simonyiszk/ZetaSDR/zetasdr-fw-stm32/Core/Inc/tusb_config.h

/*
 * The MIT License (MIT)
 *
 * Copyright (c) 2019 Ha Thach (tinyusb.org)
 *
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
 */

#ifndef _TUSB_CONFIG_H_
#define _TUSB_CONFIG_H_

#include "zetasdr_descriptor.h"

#ifdef __cplusplus
extern "C" {
#endif

//--------------------------------------------------------------------+
// Board Specific Configuration
//--------------------------------------------------------------------+

// RHPort number used for device can be defined by board.mk, default to port 0
#ifndef BOARD_TUD_RHPORT
#define BOARD_TUD_RHPORT      0
#endif

// RHPort max operational speed can defined by board.mk
#ifndef BOARD_TUD_MAX_SPEED
#define BOARD_TUD_MAX_SPEED   OPT_MODE_DEFAULT_SPEED
#endif

//--------------------------------------------------------------------
// COMMON CONFIGURATION
//--------------------------------------------------------------------

// defined by compiler flags for flexibility
#ifndef CFG_TUSB_MCU
#error CFG_TUSB_MCU must be defined
#endif

#ifndef CFG_TUSB_OS
#define CFG_TUSB_OS               OPT_OS_NONE
#endif

#ifndef CFG_TUSB_DEBUG
#define CFG_TUSB_DEBUG            0
#endif

// Enable Device stack
#define CFG_TUD_ENABLED           1

// Default is max speed that hardware controller could support with on-chip PHY
#define CFG_TUD_MAX_SPEED         BOARD_TUD_MAX_SPEED

/* USB DMA on some MCUs can only access a specific SRAM region with restriction on alignment.
 * Tinyusb use follows macros to declare transferring memory so that they can be put
 * into those specific section.
 * e.g
 * - CFG_TUSB_MEM SECTION : __attribute__ (( section(".usb_ram") ))
 * - CFG_TUSB_MEM_ALIGN   : __attribute__ ((aligned(4)))
 */
#ifndef CFG_TUSB_MEM_SECTION
#define CFG_TUSB_MEM_SECTION
#endif

#ifndef CFG_TUSB_MEM_ALIGN
#define CFG_TUSB_MEM_ALIGN        __attribute__ ((aligned(4)))
#endif

//--------------------------------------------------------------------
// DEVICE CONFIGURATION
//--------------------------------------------------------------------

#ifndef CFG_TUD_ENDPOINT0_SIZE
#define CFG_TUD_ENDPOINT0_SIZE    64
#endif

//------------- CLASS -------------//
#define CFG_TUD_AUDIO             1
#define CFG_TUD_CDC               1
#define CFG_TUD_MSC               0
#define CFG_TUD_HID               0
#define CFG_TUD_MIDI              0
#define CFG_TUD_VENDOR            0

//--------------------------------------------------------------------
// AUDIO CLASS DRIVER CONFIGURATION
//--------------------------------------------------------------------

// Have a look into audio_device.h for all configurations
#define CFG_TUD_AUDIO_FUNC_1_SAMPLE_RATE              192000

#define CFG_TUD_AUDIO_FUNC_1_DESC_LEN                 TUD_SDR_IQ_DESC_LEN //TUD_AUDIO_MIC_FOUR_CH_DESC_LEN // IQ_descriptor hossza

#define CFG_TUD_AUDIO_FUNC_1_N_AS_INT                 1
#define CFG_TUD_AUDIO_FUNC_1_CTRL_BUF_SZ              64

#define CFG_TUD_AUDIO_ENABLE_EP_IN                    1
#define CFG_TUD_AUDIO_FUNC_1_N_BYTES_PER_SAMPLE_TX    2         // This value is not required by the driver, it parses this information from the descriptor once the alternate interface is set by the host - we use it for the setup
#define CFG_TUD_AUDIO_FUNC_1_N_CHANNELS_TX            2         // This value is not required by the driver, it parses this information from the descriptor once the alternate interface is set by the host - we use it for the setup
#define CFG_TUD_AUDIO_EP_SZ_IN                        TUD_AUDIO_EP_SIZE(CFG_TUD_AUDIO_FUNC_1_SAMPLE_RATE, CFG_TUD_AUDIO_FUNC_1_N_BYTES_PER_SAMPLE_TX, CFG_TUD_AUDIO_FUNC_1_N_CHANNELS_TX)

#define CFG_TUD_AUDIO_ENABLE_ENCODING                 0
#define CFG_TUD_AUDIO_EP_IN_FLOW_CONTROL              1

#if CFG_TUD_AUDIO_ENABLE_ENCODING

#define CFG_TUD_AUDIO_FUNC_1_EP_IN_SZ_MAX             CFG_TUD_AUDIO_EP_SZ_IN
#define CFG_TUD_AUDIO_FUNC_1_EP_IN_SW_BUF_SZ          CFG_TUD_AUDIO_EP_SZ_IN

#define CFG_TUD_AUDIO_ENABLE_TYPE_I_ENCODING          1
#define CFG_TUD_AUDIO_FUNC_1_CHANNEL_PER_FIFO_TX      2         // One I2S stream contains two channels, each stream is saved within one support FIFO - this value is currently fixed, the driver does not support a changing value
#define CFG_TUD_AUDIO_FUNC_1_N_TX_SUPP_SW_FIFO        (CFG_TUD_AUDIO_FUNC_1_N_CHANNELS_TX / CFG_TUD_AUDIO_FUNC_1_CHANNEL_PER_FIFO_TX)
#define CFG_TUD_AUDIO_FUNC_1_TX_SUPP_SW_FIFO_SZ       (TUD_OPT_HIGH_SPEED ? 32 : 4) * (CFG_TUD_AUDIO_EP_SZ_IN / CFG_TUD_AUDIO_FUNC_1_N_TX_SUPP_SW_FIFO) // Example write FIFO every 1ms, so it should be 8 times larger for HS device

#else

#define CFG_TUD_AUDIO_FUNC_1_EP_IN_SZ_MAX             CFG_TUD_AUDIO_EP_SZ_IN
#define CFG_TUD_AUDIO_FUNC_1_EP_IN_SW_BUF_SZ          (TUD_OPT_HIGH_SPEED ? 32 : 4) * CFG_TUD_AUDIO_EP_SZ_IN // Example write FIFO every 1ms, so it should be 8 times larger for HS device

#endif

// CDC FIFO size of TX and RX
#define CFG_TUD_CDC_RX_BUFSIZE                    64
#define CFG_TUD_CDC_TX_BUFSIZE                    64

#ifdef __cplusplus
}
#endif

#endif /* _TUSB_CONFIG_H_ */
