simonyiszk/ZetaSDR/zetasdr-fw-stm32/Core/Src/audio.c

#include "tusb.h"
#include "audio.h"
#include "adc.h"
#include "tim.h"

//--------------------------------------------------------------------+
// AUDIO Task
//--------------------------------------------------------------------+

// Audio controls
// Current states
bool mute[CFG_TUD_AUDIO_FUNC_1_N_CHANNELS_TX + 1]; 				        // +1 for master channel 0
uint16_t volume[CFG_TUD_AUDIO_FUNC_1_N_CHANNELS_TX + 1]; 					// +1 for master channel 0
uint32_t sampFreq;
uint8_t clkValid;

// Range states
audio_control_range_2_n_t(1) volumeRng[CFG_TUD_AUDIO_FUNC_1_N_CHANNELS_TX+1]; 			// Volume range state
audio_control_range_4_n_t(1) sampleFreqRng; 						// Sample frequency range state

#if CFG_TUD_AUDIO_ENABLE_ENCODING
// Audio test data, each buffer contains 2 channels, buffer[0] for CH0-1, buffer[1] for CH1-2
uint16_t i2s_dummy_buffer[CFG_TUD_AUDIO_FUNC_1_N_TX_SUPP_SW_FIFO][CFG_TUD_AUDIO_FUNC_1_N_CHANNELS_TX*CFG_TUD_AUDIO_FUNC_1_SAMPLE_RATE/1000/CFG_TUD_AUDIO_FUNC_1_N_TX_SUPP_SW_FIFO];
#else
// Audio data, double buffering to reduce glitches
volatile uint16_t buffer_a[CFG_TUD_AUDIO_FUNC_1_N_CHANNELS_TX*CFG_TUD_AUDIO_FUNC_1_SAMPLE_RATE/1000];
volatile uint16_t buffer_b[CFG_TUD_AUDIO_FUNC_1_N_CHANNELS_TX*CFG_TUD_AUDIO_FUNC_1_SAMPLE_RATE/1000];
volatile uint16_t *buf_record, *buf_stream;
#endif

void audio_init(void){
  
  sampFreq = AUDIO_SAMPLE_RATE;
  clkValid = 1;

  sampleFreqRng.wNumSubRanges = 1;
  sampleFreqRng.subrange[0].bMin = AUDIO_SAMPLE_RATE;
  sampleFreqRng.subrange[0].bMax = AUDIO_SAMPLE_RATE;
  sampleFreqRng.subrange[0].bRes = 0;

  // Generate dummy data
#if CFG_TUD_AUDIO_ENABLE_ENCODING
  uint16_t * p_buff = i2s_dummy_buffer[0];
  uint16_t dataVal = 0;
  for (uint16_t cnt = 0; cnt < AUDIO_SAMPLE_RATE/1000; cnt++)
  {
    // CH0 saw wave
    *p_buff++ = dataVal;
    // CH1 inverted saw wave
    *p_buff++ = 3200 + AUDIO_SAMPLE_RATE/1000 - dataVal;
    dataVal+= 32;
  }
  p_buff = i2s_dummy_buffer[1];
  for (uint16_t cnt = 0; cnt < AUDIO_SAMPLE_RATE/1000; cnt++)
  {
    // CH3 square wave
    *p_buff++ = cnt < (AUDIO_SAMPLE_RATE/1000/2) ? 3400:5000;
    // CH4 sinus wave
    float t = 2*3.1415f * cnt / (AUDIO_SAMPLE_RATE/1000);
    *p_buff++ = (uint16_t)((int16_t)(sinf(t) * 750) + 6000);
  }
#else
  // generating test data, not used 
  volatile uint16_t * p_buff = buffer_a;
  //uint16_t dataVal = 0;
  for (uint16_t cnt = 0; cnt < AUDIO_SAMPLE_RATE/1000; cnt++)
  {
    // CH0 saw wave
    //*p_buff++ = dataVal;
    // CH1 inverted saw wave
    //*p_buff++ = 3200 + AUDIO_SAMPLE_RATE/1000 - dataVal;
    //dataVal+= 32;
    // CH3 square wave
    *p_buff++ = cnt < (AUDIO_SAMPLE_RATE/1000/2) ? 3400:5000;
    // CH4 sinus wave
    float t = 2*3.1415f * cnt / (AUDIO_SAMPLE_RATE/1000);
    *p_buff++ = (uint16_t)((int16_t)(sinf(t) * 750) + 6000);
  }
#endif
  buf_record = buffer_a;
  buf_stream = buffer_b;
}

// use something like this if more then one ADC is available
/*void HAL_ADC_ConvCpltCallback(ADC_HandleTypeDef *hadc){

  volatile uint16_t * p_buff = i2s_dummy_buffer;
  static uint16_t idx = 0;

  uint32_t CH0 = HAL_ADC_GetValue(&hadc1) & 0x0000FFFF;
  uint32_t CH1 = HAL_ADC_GetValue(&hadc1) & 0x0000FFFF;

  p_buff[idx] = (uint16_t) CH0;
  p_buff[idx+1] = (uint16_t) CH1;

  if(idx > CFG_TUD_AUDIO_FUNC_1_N_CHANNELS_TX*CFG_TUD_AUDIO_FUNC_1_SAMPLE_RATE/1000){
    idx = 0;
  }else{
    idx+=2;
  }
}*/

volatile uint8_t sample_count = 0;
volatile bool transfer_completed = false;

// Sample IN0
void HAL_ADC_ConvCpltCallback(ADC_HandleTypeDef *hadc){  
  uint16_t adc_val = ((uint16_t) HAL_ADC_GetValue(hadc)) - 0x8000u;
  buf_record[sample_count << 1] = adc_val;
}

// Sample IN1
void HAL_ADCEx_InjectedConvCpltCallback(ADC_HandleTypeDef *hadc){
  uint16_t adc_val = ((uint16_t) HAL_ADCEx_InjectedGetValue(hadc, ADC_INJECTED_RANK_1) << 1) - 0x8000u; // shift is needed, see the reference manual
  buf_record[(sample_count << 1) | 1] = adc_val;
  sample_count++;
  if(sample_count >= AUDIO_SAMPLE_RATE / 1000){
    sample_count = 0;
    transfer_completed = true;
  }
}

void audio_task(void)
{
  if(!transfer_completed) return;
  transfer_completed = false;

  if(buf_record == buffer_a){ // buffer swap
    buf_record = buffer_b;
    buf_stream = buffer_a;
  }else{
    buf_record = buffer_a;
    buf_stream = buffer_b;
  }

#if CFG_TUD_AUDIO_ENABLE_ENCODING
  // Write I2S buffer into FIFO
  for (uint8_t cnt=0; cnt < 2; cnt++)
  {
    tud_audio_write_support_ff(cnt, i2s_dummy_buffer[cnt], AUDIO_SAMPLE_RATE/1000 * CFG_TUD_AUDIO_FUNC_1_N_BYTES_PER_SAMPLE_TX * CFG_TUD_AUDIO_FUNC_1_CHANNEL_PER_FIFO_TX);
  }

  /* itt kéne dupla bufferelni
  static float phi = 0;
  uint16_t * p_buff = i2s_dummy_buffer[1];
  for (uint16_t cnt = 0; cnt < AUDIO_SAMPLE_RATE/1000; cnt++)
  {
    // CH3 square wave
    *p_buff++ = cnt < (AUDIO_SAMPLE_RATE/1000/2) ? 3400:5000;
    // CH4 sinus wave
    phi += 2*3.1415f / (AUDIO_SAMPLE_RATE/333);
    if(phi>2*3.1415f) phi -= 2* 3.1415f;
    *p_buff++ = (uint16_t)((int16_t)(sinf(phi) * 750) + 6000);
  }
  eddig */ 

#else
  tud_audio_write((void*) buf_stream, AUDIO_SAMPLE_RATE/1000 * CFG_TUD_AUDIO_FUNC_1_N_BYTES_PER_SAMPLE_TX * CFG_TUD_AUDIO_FUNC_1_N_CHANNELS_TX);
#endif
}

//--------------------------------------------------------------------+
// Application Callback API Implementations
//--------------------------------------------------------------------+

// Invoked when audio class specific set request received for an EP
bool tud_audio_set_req_ep_cb(uint8_t rhport, tusb_control_request_t const * p_request, uint8_t *pBuff)
{
  (void) rhport;
  (void) pBuff;

  // We do not support any set range requests here, only current value requests
  TU_VERIFY(p_request->bRequest == AUDIO_CS_REQ_CUR);

  // Page 91 in UAC2 specification
  uint8_t channelNum = TU_U16_LOW(p_request->wValue);
  uint8_t ctrlSel = TU_U16_HIGH(p_request->wValue);
  uint8_t ep = TU_U16_LOW(p_request->wIndex);

  (void) channelNum; (void) ctrlSel; (void) ep;

  return false; 	// Yet not implemented
}

// Invoked when audio class specific set request received for an interface
bool tud_audio_set_req_itf_cb(uint8_t rhport, tusb_control_request_t const * p_request, uint8_t *pBuff)
{
  (void) rhport;
  (void) pBuff;

  // We do not support any set range requests here, only current value requests
  TU_VERIFY(p_request->bRequest == AUDIO_CS_REQ_CUR);

  // Page 91 in UAC2 specification
  uint8_t channelNum = TU_U16_LOW(p_request->wValue);
  uint8_t ctrlSel = TU_U16_HIGH(p_request->wValue);
  uint8_t itf = TU_U16_LOW(p_request->wIndex);

  (void) channelNum; (void) ctrlSel; (void) itf;

  return false; 	// Yet not implemented
}

// Invoked when audio class specific set request received for an entity
bool tud_audio_set_req_entity_cb(uint8_t rhport, tusb_control_request_t const * p_request, uint8_t *pBuff)
{
  (void) rhport;

  // Page 91 in UAC2 specification
  uint8_t channelNum = TU_U16_LOW(p_request->wValue);
  uint8_t ctrlSel = TU_U16_HIGH(p_request->wValue);
  uint8_t itf = TU_U16_LOW(p_request->wIndex);
  uint8_t entityID = TU_U16_HIGH(p_request->wIndex);

  (void) itf;

  // We do not support any set range requests here, only current value requests
  TU_VERIFY(p_request->bRequest == AUDIO_CS_REQ_CUR);

  // If request is for our feature unit
  if ( entityID == 2 )
  {
    switch ( ctrlSel )
    {
      case AUDIO_FU_CTRL_MUTE:
        // Request uses format layout 1
        TU_VERIFY(p_request->wLength == sizeof(audio_control_cur_1_t));

        mute[channelNum] = ((audio_control_cur_1_t*) pBuff)->bCur;

        TU_LOG2("    Set Mute: %d of channel: %u\r\n", mute[channelNum], channelNum);
      return true;

      case AUDIO_FU_CTRL_VOLUME:
        // Request uses format layout 2
        TU_VERIFY(p_request->wLength == sizeof(audio_control_cur_2_t));

        volume[channelNum] = (uint16_t) ((audio_control_cur_2_t*) pBuff)->bCur;

        TU_LOG2("    Set Volume: %d dB of channel: %u\r\n", volume[channelNum], channelNum);
      return true;

        // Unknown/Unsupported control
      default:
        TU_BREAKPOINT();
      return false;
    }
  }
  return false;    // Yet not implemented
}

// Invoked when audio class specific get request received for an EP
bool tud_audio_get_req_ep_cb(uint8_t rhport, tusb_control_request_t const * p_request)
{
  (void) rhport;

  // Page 91 in UAC2 specification
  uint8_t channelNum = TU_U16_LOW(p_request->wValue);
  uint8_t ctrlSel = TU_U16_HIGH(p_request->wValue);
  uint8_t ep = TU_U16_LOW(p_request->wIndex);

  (void) channelNum; (void) ctrlSel; (void) ep;

  //	return tud_control_xfer(rhport, p_request, &tmp, 1);

  return false; 	// Yet not implemented
}

// Invoked when audio class specific get request received for an interface
bool tud_audio_get_req_itf_cb(uint8_t rhport, tusb_control_request_t const * p_request)
{
  (void) rhport;

  // Page 91 in UAC2 specification
  uint8_t channelNum = TU_U16_LOW(p_request->wValue);
  uint8_t ctrlSel = TU_U16_HIGH(p_request->wValue);
  uint8_t itf = TU_U16_LOW(p_request->wIndex);

  (void) channelNum; (void) ctrlSel; (void) itf;

  return false; 	// Yet not implemented
}

// Invoked when audio class specific get request received for an entity
bool tud_audio_get_req_entity_cb(uint8_t rhport, tusb_control_request_t const * p_request)
{
  (void) rhport;

  // Page 91 in UAC2 specification
  uint8_t channelNum = TU_U16_LOW(p_request->wValue);
  uint8_t ctrlSel = TU_U16_HIGH(p_request->wValue);
  // uint8_t itf = TU_U16_LOW(p_request->wIndex); 			// Since we have only one audio function implemented, we do not need the itf value
  uint8_t entityID = TU_U16_HIGH(p_request->wIndex);

  // Input terminal (Microphone input)
  if (entityID == 1)
  {
    switch ( ctrlSel )
    {
      case AUDIO_TE_CTRL_CONNECTOR:
      {
        // The terminal connector control only has a get request with only the CUR attribute.
        audio_desc_channel_cluster_t ret;

        // Those are dummy values for now
        ret.bNrChannels = 1;
        ret.bmChannelConfig = (audio_channel_config_t) 0;
        ret.iChannelNames = 0;

        TU_LOG2("    Get terminal connector\r\n");

        return tud_audio_buffer_and_schedule_control_xfer(rhport, p_request, (void*) &ret, sizeof(ret));
      }
      break;

        // Unknown/Unsupported control selector
      default:
        TU_BREAKPOINT();
        return false;
    }
  }

  // Feature unit
  if (entityID == 2)
  {
    switch ( ctrlSel )
    {
      case AUDIO_FU_CTRL_MUTE:
        // Audio control mute cur parameter block consists of only one byte - we thus can send it right away
        // There does not exist a range parameter block for mute
        TU_LOG2("    Get Mute of channel: %u\r\n", channelNum);
        return tud_control_xfer(rhport, p_request, &mute[channelNum], 1);

      case AUDIO_FU_CTRL_VOLUME:
        switch ( p_request->bRequest )
        {
          case AUDIO_CS_REQ_CUR:
            TU_LOG2("    Get Volume of channel: %u\r\n", channelNum);
            return tud_control_xfer(rhport, p_request, &volume[channelNum], sizeof(volume[channelNum]));

          case AUDIO_CS_REQ_RANGE:
            TU_LOG2("    Get Volume range of channel: %u\r\n", channelNum);

            // Copy values - only for testing - better is version below
            audio_control_range_2_n_t(1)
            ret;

            ret.wNumSubRanges = 1;
            ret.subrange[0].bMin = -90;           // -90 dB
            ret.subrange[0].bMax = 90;		// +90 dB
            ret.subrange[0].bRes = 1; 		// 1 dB steps

            return tud_audio_buffer_and_schedule_control_xfer(rhport, p_request, (void*) &ret, sizeof(ret));

            // Unknown/Unsupported control
          default:
            TU_BREAKPOINT();
            return false;
        }
      break;

        // Unknown/Unsupported control
      default:
        TU_BREAKPOINT();
        return false;
    }
  }

  // Clock Source unit
  if ( entityID == 4 )
  {
    switch ( ctrlSel )
    {
      case AUDIO_CS_CTRL_SAM_FREQ:
        // channelNum is always zero in this case
        switch ( p_request->bRequest )
        {
          case AUDIO_CS_REQ_CUR:
            TU_LOG2("    Get Sample Freq.\r\n");
            // Buffered control transfer is needed for IN flow control to work
            return tud_audio_buffer_and_schedule_control_xfer(rhport, p_request, &sampFreq, sizeof(sampFreq));

          case AUDIO_CS_REQ_RANGE:
            TU_LOG2("    Get Sample Freq. range\r\n");
            return tud_control_xfer(rhport, p_request, &sampleFreqRng, sizeof(sampleFreqRng));

           // Unknown/Unsupported control
          default:
            TU_BREAKPOINT();
            return false;
        }
      break;

      case AUDIO_CS_CTRL_CLK_VALID:
        // Only cur attribute exists for this request
        TU_LOG2("    Get Sample Freq. valid\r\n");
        return tud_control_xfer(rhport, p_request, &clkValid, sizeof(clkValid));

      // Unknown/Unsupported control
      default:
        TU_BREAKPOINT();
        return false;
    }
  }

  TU_LOG2("  Unsupported entity: %d\r\n", entityID);
  return false; 	// Yet not implemented
}

bool tud_audio_tx_done_pre_load_cb(uint8_t rhport, uint8_t itf, uint8_t ep_in, uint8_t cur_alt_setting)
{
  (void) rhport;
  (void) itf;
  (void) ep_in;
  (void) cur_alt_setting;


  // In read world application data flow is driven by I2S clock,
  // both tud_audio_tx_done_pre_load_cb() & tud_audio_tx_done_post_load_cb() are hardly used.
  // For example in your I2S receive callback:
  // void I2S_Rx_Callback(int channel, const void* data, uint16_t samples)
  // {
  //    tud_audio_write_support_ff(channel, data, samples * N_BYTES_PER_SAMPLE * N_CHANNEL_PER_FIFO);
  // }

  return true;
}

bool tud_audio_tx_done_post_load_cb(uint8_t rhport, uint16_t n_bytes_copied, uint8_t itf, uint8_t ep_in, uint8_t cur_alt_setting)
{
  (void) rhport;
  (void) n_bytes_copied;
  (void) itf;
  (void) ep_in;
  (void) cur_alt_setting;

  return true;
}

bool tud_audio_set_itf_close_EP_cb(uint8_t rhport, tusb_control_request_t const * p_request)
{
  (void) rhport;
  (void) p_request;

  return true;
}
