simonyiszk/ZetaSDR/zetasdr-fw/src/tim.c

#include "tim.h"

/*********************************************************************
 * @brief   Timer1 initialization routine. 
 * @return  none
 */
void TIM1_OutCompare_Init(uint16_t arr, uint16_t psc, uint16_t ccp)
{
	GPIO_InitTypeDef GPIO_InitStructure={0};
	TIM_OCInitTypeDef TIM_OCInitStructure={0};
	TIM_TimeBaseInitTypeDef TIM_TimeBaseInitStructure={0};

	RCC_APB2PeriphClockCmd( RCC_APB2Periph_GPIOA | RCC_APB2Periph_TIM1, ENABLE );

	GPIO_InitStructure.GPIO_Pin = GPIO_Pin_8;           // timer output on PA8
	GPIO_InitStructure.GPIO_Mode = GPIO_Mode_AF_PP;
	GPIO_InitStructure.GPIO_Speed = GPIO_Speed_50MHz;
	GPIO_Init( GPIOA, &GPIO_InitStructure );

	TIM_TimeBaseInitStructure.TIM_Period = arr;
	TIM_TimeBaseInitStructure.TIM_Prescaler = psc;
	TIM_TimeBaseInitStructure.TIM_ClockDivision = TIM_CKD_DIV1;
	TIM_TimeBaseInitStructure.TIM_CounterMode = TIM_CounterMode_Up;
	TIM_TimeBaseInit( TIM1, &TIM_TimeBaseInitStructure);

	TIM_OCInitStructure.TIM_OCMode = TIM_OCMode_PWM1;
	TIM_OCInitStructure.TIM_OutputState = TIM_OutputState_Enable;
	TIM_OCInitStructure.TIM_Pulse = ccp;
	TIM_OCInitStructure.TIM_OCPolarity = TIM_OCPolarity_High;
	TIM_OC1Init( TIM1, &TIM_OCInitStructure );

	TIM_CtrlPWMOutputs(TIM1, ENABLE );
	TIM_OC1PreloadConfig( TIM1, TIM_OCPreload_Disable );
	TIM_ARRPreloadConfig( TIM1, ENABLE );
}
